AlwaysAbia/DesktopBuddyRobot/BuddyBotFirmware/include/secrets.example.h

// Copy this file to include/secrets.h and fill in your network credentials.
// include/secrets.h is gitignored so credentials never get committed.
#pragma once

#define WIFI_SSID     ""
#define WIFI_PASSWORD ""

// ThingsBoard device access token (device "buddybot-01" -> "Copy access token").
#define TB_ACCESS_TOKEN ""
